marco-luzzara/floor-cleaner/cleaner/Core/Inc/driving.h

#ifndef INC_DRIVING_H_
#define INC_DRIVING_H_

#include <stdbool.h>
#include "types/map.h"
#include "types/cleaner.h"
#include "lcd.h"

/**
 * @brief starts to drive
 * @retval 0 - the cleaner completed the cleaning process
 * 				 1 - cleaner not found
 * 				 2 - start position does not exist
 * 				 3 - start position cannot be reached
 * 				 4 - cannot reach a cell because surrounded by unavailable cells
 */
int start_drive(MapInfo* mapInfo,
								bool* obstacle_found,
								UART_HandleTypeDef *huart,
								Lcd_HandleTypeDef* lcd,
								MotorsInfo* motorsInfo,
								CleanComponentsInfo* cleanComponentsInfo);

/**
 * @brief signals that the cleaner has finished its work
 */
//void end_drive();

#endif /* INC_DRIVING_H_ */
