marco-luzzara/floor-cleaner/cleaner/Core/Src/lcd.c

/*
 * lcd.c (from https://github.com/4ilo/HD44780-Stm32HAL/tree/master/lcd_lib)
 *
 *  Created on: 10/06/2018
 *      Author: Olivier Van den Eede
 */

#include "lcd.h"
#include <string.h>

const uint8_t ROW_16[] = {0x00, 0x40, 0x10, 0x50};
const uint8_t ROW_20[] = {0x00, 0x40, 0x14, 0x54};
/************************************** Static declarations **************************************/

static void lcd_write_data(Lcd_HandleTypeDef * lcd, uint8_t data);
static void lcd_write_command(Lcd_HandleTypeDef * lcd, uint8_t command);
static void lcd_write(Lcd_HandleTypeDef * lcd, uint8_t data, uint8_t len);


/************************************** Function definitions **************************************/

/**
 * Create new Lcd_HandleTypeDef and initialize the Lcd
 */
Lcd_HandleTypeDef Lcd_create(
		Lcd_PortType port[], Lcd_PinType pin[],
		Lcd_PortType rs_port, Lcd_PinType rs_pin,
		Lcd_PortType en_port, Lcd_PinType en_pin, Lcd_ModeTypeDef mode)
{
	Lcd_HandleTypeDef lcd;

	lcd.mode = mode;

	lcd.en_pin = en_pin;
	lcd.en_port = en_port;

	lcd.rs_pin = rs_pin;
	lcd.rs_port = rs_port;

	lcd.data_pin = pin;
	lcd.data_port = port;

	Lcd_init(&lcd);

	return lcd;
}

/**
 * Initialize 16x2-lcd without cursor
 */
void Lcd_init(Lcd_HandleTypeDef * lcd)
{
	if(lcd->mode == LCD_4_BIT_MODE)
	{
			lcd_write_command(lcd, 0x33);
			lcd_write_command(lcd, 0x32);
			lcd_write_command(lcd, FUNCTION_SET | OPT_N);				// 4-bit mode
	}
	else
		lcd_write_command(lcd, FUNCTION_SET | OPT_DL | OPT_N);


	lcd_write_command(lcd, CLEAR_DISPLAY);						// Clear screen
	lcd_write_command(lcd, DISPLAY_ON_OFF_CONTROL | OPT_D);		// Lcd-on, cursor-off, no-blink
	lcd_write_command(lcd, ENTRY_MODE_SET | OPT_INC);			// Increment cursor
}

/**
 * Write a number on the current position
 */
void Lcd_int(Lcd_HandleTypeDef * lcd, int number)
{
	char buffer[11];
	sprintf(buffer, "%d", number);

	Lcd_string(lcd, buffer);
}

/**
 * Write a string on the current position
 */
void Lcd_string(Lcd_HandleTypeDef * lcd, const char * string)
{
	for(uint8_t i = 0; i < strlen(string); i++)
	{
		lcd_write_data(lcd, string[i]);
	}
}

/**
 * Set the cursor position
 */
void Lcd_cursor(Lcd_HandleTypeDef * lcd, uint8_t row, uint8_t col)
{
	#ifdef LCD20xN
	lcd_write_command(lcd, SET_DDRAM_ADDR + ROW_20[row] + col);
	#endif

	#ifdef LCD16xN
	lcd_write_command(lcd, SET_DDRAM_ADDR + ROW_16[row] + col);
	#endif
}

/**
 * Clear the screen
 */
void Lcd_clear(Lcd_HandleTypeDef * lcd) {
	lcd_write_command(lcd, CLEAR_DISPLAY);
}

void Lcd_define_char(Lcd_HandleTypeDef * lcd, uint8_t code, uint8_t bitmap[]){
	lcd_write_command(lcd, SETCGRAM_ADDR + (code << 3));
	for(uint8_t i=0;i<8;++i){
		lcd_write_data(lcd, bitmap[i]);
	}

}


/************************************** Static function definition **************************************/

/**
 * Write a byte to the command register
 */
void lcd_write_command(Lcd_HandleTypeDef * lcd, uint8_t command)
{
	HAL_GPIO_WritePin(lcd->rs_port, lcd->rs_pin, LCD_COMMAND_REG);		// Write to command register

	if(lcd->mode == LCD_4_BIT_MODE)
	{
		lcd_write(lcd, (command >> 4), LCD_NIB);
		lcd_write(lcd, command & 0x0F, LCD_NIB);
	}
	else
	{
		lcd_write(lcd, command, LCD_BYTE);
	}

}

/**
 * Write a byte to the data register
 */
void lcd_write_data(Lcd_HandleTypeDef * lcd, uint8_t data)
{
	HAL_GPIO_WritePin(lcd->rs_port, lcd->rs_pin, LCD_DATA_REG);			// Write to data register

	if(lcd->mode == LCD_4_BIT_MODE)
	{
		lcd_write(lcd, data >> 4, LCD_NIB);
		lcd_write(lcd, data & 0x0F, LCD_NIB);
	}
	else
	{
		lcd_write(lcd, data, LCD_BYTE);
	}

}

/**
 * Set len bits on the bus and toggle the enable line
 */
void lcd_write(Lcd_HandleTypeDef * lcd, uint8_t data, uint8_t len)
{
	for(uint8_t i = 0; i < len; i++)
	{
		HAL_GPIO_WritePin(lcd->data_port[i], lcd->data_pin[i], (data >> i) & 0x01);
	}

	HAL_GPIO_WritePin(lcd->en_port, lcd->en_pin, 1);
	DELAY(1);
	HAL_GPIO_WritePin(lcd->en_port, lcd->en_pin, 0); 		// Data receive on falling edge
}

/**
 * clear the entire screen and write from 0,0
 */
void Lcd_clear_and_write(Lcd_HandleTypeDef* lcd, const char* message) {
	Lcd_clear(lcd);

	const size_t message_len = strlen(message);
	if (message_len <= 16) {
		Lcd_cursor(lcd, 0, 0);
		Lcd_string(lcd, message);
	}
	else { // the message is longer than the first line maximum size (16)
		char message_p1[17]; memset(message_p1, 0, sizeof(message_p1));
		char message_p2[17]; memset(message_p2, 0, sizeof(message_p2));

		strncpy(message_p1, message, 16);
		strncpy(message_p2, message + 16 * sizeof(char), 16);

		Lcd_cursor(lcd, 0, 0);
		Lcd_string(lcd, message_p1);

		Lcd_cursor(lcd, 1, 0);
		Lcd_string(lcd, message_p2);
	}
}
